jaw0/light-stick/src/color.h

#define BH1745_ADDRESS		(0x72 >> 1)

#define BH1745_REGISTER_SYSTEM_CONTROL 0x40
#define BH1745_REGISTER_MODE_CONTROL1  0x41
#define BH1745_REGISTER_MODE_CONTROL2  0x42
#define BH1745_REGISTER_MODE_CONTROL3  0x43
#define BH1745_REGISTER_RED_LSB        0x50
#define BH1745_REGISTER_RED_MSB        0x51
#define BH1745_REGISTER_GREEN_LSB      0x52
#define BH1745_REGISTER_GREEN_MSB      0x53
#define BH1745_REGISTER_BLUE_LSB       0x54
#define BH1745_REGISTER_BLUE_MSB       0x55
#define BH1745_REGISTER_CLEAR_LSB      0x56
#define BH1745_REGISTER_CLEAR_MSB      0x57
#define BH1745_REGISTER_DINT_LSB       0x58
#define BH1745_REGISTER_DINT_MSB       0x59
#define BH1745_REGISTER_INT            0x60
#define BH1745_REGISTER_PERSISTENCE    0x61
#define BH1745_REGISTER_TH_LSB         0x62
#define BH1745_REGISTER_TH_MSB         0x63
#define BH1745_REGISTER_TL_LSB         0x64
#define BH1745_REGISTER_TL_MSB         0x65
#define BH1745_REGISTER_MANUFACTURER   0x92

#define BH1745_MANUFACTURER	0xE0
