jaw0/light-stick/src/temp.h

#define TMP100_ADDRESS_0	(0x90 >> 1)
#define TMP100_ADDRESS_1	(0x96 >> 1)
#define TMP100_ADDRESS_2	(0x98 >> 1)	// on ctl board

#define TMP100_REGISTER_TEMP	0
#define TMP100_REGISTER_CONFIG	1
#define TMP100_REGISTER_TLOW	2
#define TMP100_REGISTER_THIGH	3
