jaw0/light-stick/src/touch.h

#define CAP1298_ADDRESS		(0x50 >> 1)

#define CAP1298_REGISTER_MAIN_CONTROL          0x0
#define CAP1298_REGISTER_GENERAL_STATUS	       0x2
#define CAP1298_REGISTER_INPUT_STATUS	       0x3
#define CAP1298_REGISTER_NOISE_STATUS	       0xA

#define CAP1298_REGISTER_SENSITIVITY           0x1F
#define CAP1298_REGISTER_CONFIG                0x20
#define CAP1298_REGISTER_INPUT_ENABLE          0x21
#define CAP1298_REGISTER_INPUT_CONFIG          0x22
#define CAP1298_REGISTER_INPUT_CONFIG2         0x23
#define CAP1298_REGISTER_AVESAMP_CONFIG        0x24
#define CAP1298_REGISTER_CALIBRATION           0x26
#define CAP1298_REGISTER_INTERRUPT_ENABLE      0x27
#define CAP1298_REGISTER_REPEAT_ENABLE         0x28
#define CAP1298_REGISTER_GUARD_ENABLE          0x29
#define CAP1298_REGISTER_MULTI_TOUCH_CONFIG    0x2A
#define CAP1298_REGISTER_MULTI_PATTERN_CONFIG  0x2B
#define CAP1298_REGISTER_MULTI_TOUCH_PATTERN   0x2D
#define CAP1298_REGISTER_RECALIB_CONFIG        0x2F
#define CAP1298_REGISTER_INPUT1_THRESHOLD      0x30
#define CAP1298_REGISTER_INPUT2_THRESHOLD      0x31
#define CAP1298_REGISTER_INPUT3_THRESHOLD      0x32
#define CAP1298_REGISTER_INPUT4_THRESHOLD      0x33
#define CAP1298_REGISTER_INPUT5_THRESHOLD      0x34
#define CAP1298_REGISTER_INPUT6_THRESHOLD      0x35
#define CAP1298_REGISTER_INPUT7_THRESHOLD      0x36
#define CAP1298_REGISTER_INPUT8_THRESHOLD      0x37
#define CAP1298_REGISTER_INPUT_NOISE_THRESHOLD 0x38
#define CAP1298_REGISTER_STANDBY_CHANNEL       0x40
#define CAP1298_REGISTER_STANDBY_CONFIG        0x41
#define CAP1298_REGISTER_STANDBY_SENSITIVITY   0x42
#define CAP1298_REGISTER_STANDBY_THRESHOLD     0x43
#define CAP1298_REGISTER_CONFIG2               0x44

#define CAP1298_REGISTER_PRODUCT_ID            0xFD
#define CAP1298_REGISTER_MANUFACTURER          0xFE
#define CAP1298_REGISTER_REVISION              0xFF

#define CAP1298_PRODUCT_ID	0x71
#define CAP1298_MANUFACTURER	0x71
