jaw0/light-stick/src/util.h

/*
  Copyright (c) 2014
  Author: Jeff Weisberg <jaw @ tcp4me.com>
  Created: 2014-May-15 13:31 (EDT)
  Function: 

*/
#ifndef __util_h__
#define __util_h__

#define ABS(a)                	(((a)<0)?-(a):(a))
#define MIN(a,b)        	(((a)<(b)) ? (a) : (b))
#define MAX(a,b)        	(((a)>(b)) ? (a) : (b))

struct KeyValue {
    const char *name;
    int value;
};

typedef char bool;

extern unsigned int random(void);

#define set_font(f)	fioctl(STDOUT, IOC_GFXFONTNAME, f)

#endif /* __util_h__ */
